marcvty98/MD/Designs/Diseños para el Sistema de Locomocion/wheel/wheel.SLDPRT

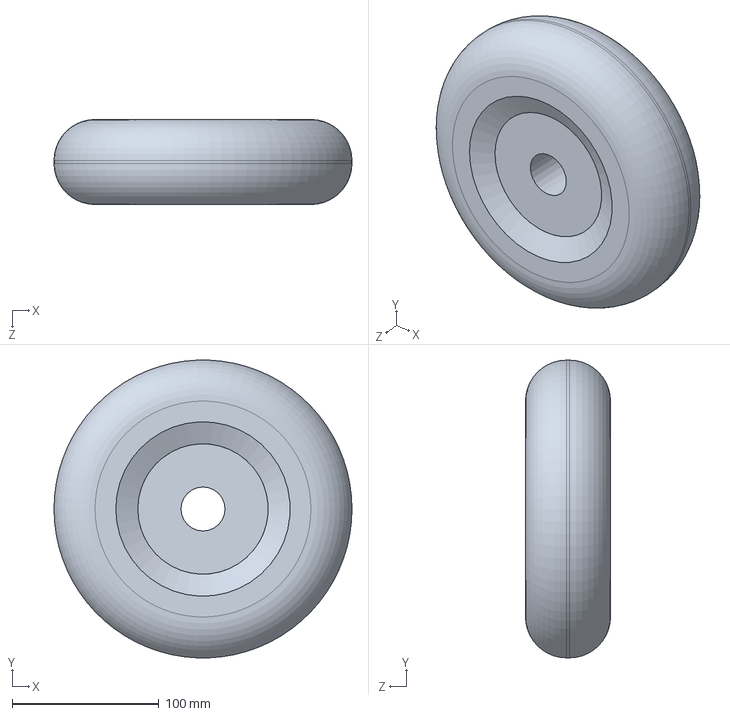
[picture p22: CAD file, 2022-02-10]
Designs/Diseños para el Sistema de Locomocion/wheel/wheel.SLDPRT
203.2 x 203.0 x 58.0 mm
