marcvty98/MD/src/mobile_robot_autonomous_navigation/stl/RpLidar.stl

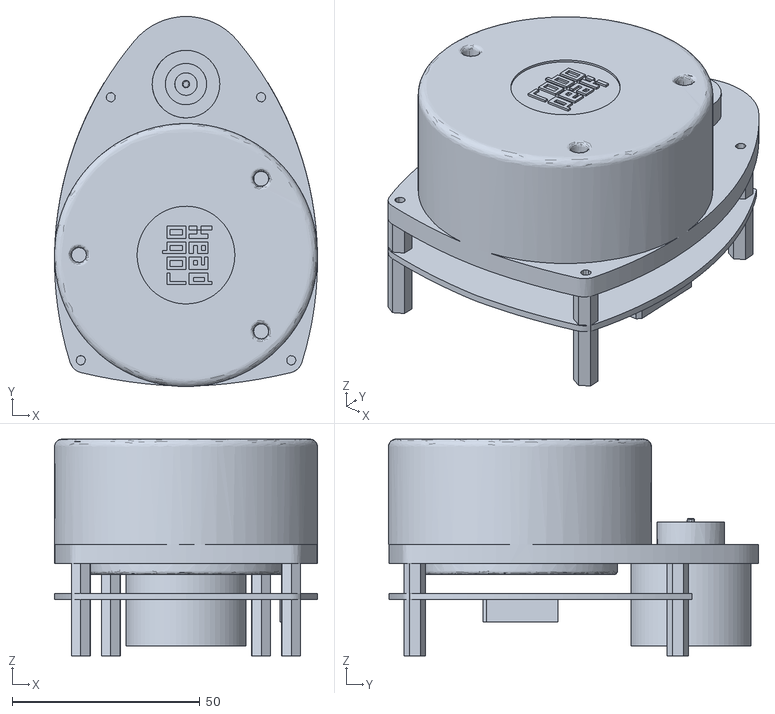
[picture p23: CAD file, 2022-02-10]
src/mobile_robot_autonomous_navigation/stl/RpLidar.stl
70.0 x 98.5 x 57.7
