marcvty98/MD/Designs/Diseño para el Sistema de conteo/Ranura/ranura.SLDPRT

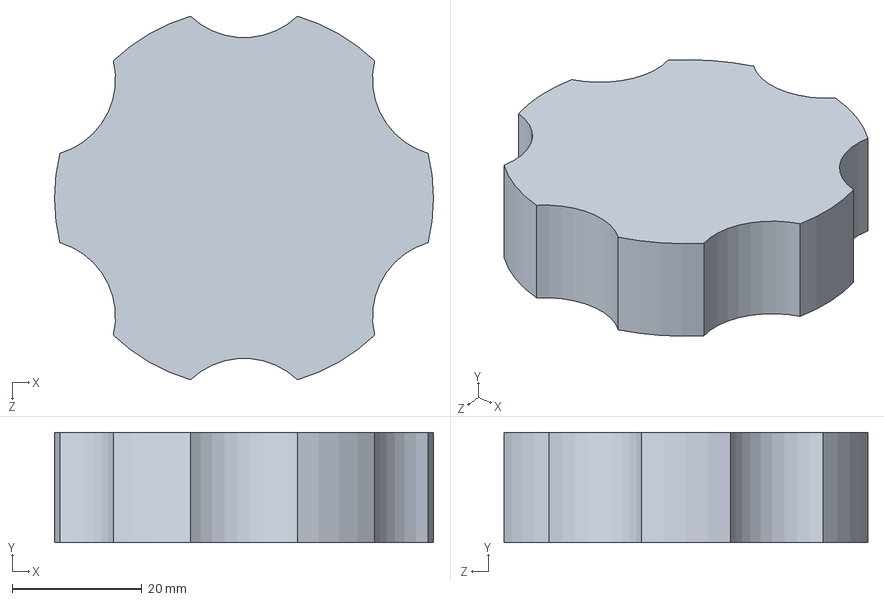
[picture p24: CAD file, 2022-02-10]
Designs/Diseño para el Sistema de conteo/Ranura/ranura.SLDPRT
58.5 x 17.0 x 56.1 mm
